MaVILab-UFV/FPVCar_LARS-2025/software/tests/distancia/data/test_03m.csv

timestamp | latencia | fps
1734579958.9551 | 0.04106402397155762 | 5.765084479601648e-10
1734579958.9595 | 0.04106402397155762 | 290.72599986137106
1734579959.0578 | 0.04106402397155762 | 10.174422666407917
1734579959.1672 | 0.04106402397155762 | 9.142657848732023
1734579959.2630 | 0.04106402397155762 | 10.430737857800105
1734579959.3745 | 0.04106402397155762 | 8.973673569376189
1734579959.4856 | 0.04106402397155762 | 9.003318579321773
1734579959.5805 | 0.04106402397155762 | 10.529166488850285
1734579959.7069 | 0.04106402397155762 | 7.913034619375531
1734579959.7789 | 0.015756845474243164 | 13.88276960046074
1734579959.9258 | 0.015756845474243164 | 6.808614529510786
1734579960.0048 | 0.015756845474243164 | 12.659871357985192
1734579960.1151 | 0.015756845474243164 | 9.066569825253127
1734579960.2270 | 0.015756845474243164 | 8.93728585309309
1734579960.3223 | 0.015756845474243164 | 10.487647776599788
1734579960.4328 | 0.015756845474243164 | 9.050625017532427
1734579960.5440 | 0.015756845474243164 | 8.992200463941618
1734579960.6553 | 0.015756845474243164 | 8.990118873594458
1734579960.7493 | 0.015756845474243164 | 10.62855463147385
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
