MaVILab-UFV/FPVCar_LARS-2025/software/tests/distancia/data/test_04m.csv

timestamp | latencia | fps
1734580084.0002 | 0.031940460205078125 | 5.765084063999112e-10
1734580084.0069 | 0.031940460205078125 | 150.04307075910424
1734580084.1037 | 0.031940460205078125 | 10.33504914583092
1734580084.2382 | 0.031940460205078125 | 7.431675709005603
1734580084.2545 | 0.031940460205078125 | 61.56595769665478
1734580084.4295 | 0.031940460205078125 | 5.712084936931931
1734580084.5248 | 0.031940460205078125 | 10.496965510682653
1734580084.6359 | 0.031940460205078125 | 9.000439903779096
1734580084.7469 | 0.031940460205078125 | 9.00944914025497
1734580084.8426 | 0.031940460205078125 | 10.445648708957602
1734580084.8905 | 0.031940460205078125 | 20.874038241412602
1734580085.0506 | 0.031940460205078125 | 6.245752704584205
1734580085.1991 | 0.031270742416381836 | 6.734256965372629
1734580085.2659 | 0.031270742416381836 | 14.987418484572368
1734580085.3809 | 0.031270742416381836 | 8.695759621345154
1734580085.3971 | 0.031270742416381836 | 61.519903781278416
1734580085.5723 | 0.031270742416381836 | 5.708019362854837
1734580085.6675 | 0.031270742416381836 | 10.504089636415545
1734580085.7787 | 0.031270742416381836 | 8.99202696126248
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
