MaVILab-UFV/FPVCar_LARS-2025/software/tests/distancia/data/test_05m.csv

timestamp | latencia | fps
1734580281.2012 | 0.03157162666320801 | 5.765083408578247e-10
1734580281.2151 | 0.03157162666320801 | 72.12160396175803
1734580281.3469 | 0.03157162666320801 | 7.585349797811006
1734580281.4347 | 0.03157162666320801 | 11.389672916864672
1734580281.5637 | 0.03157162666320801 | 7.750451337752162
1734580281.6619 | 0.03157162666320801 | 10.181486282449011
1734580281.7575 | 0.03157162666320801 | 10.462794166803866
1734580281.8525 | 0.03157162666320801 | 10.522905857677602
1734580281.9582 | 0.015758752822875977 | 9.46607445924963
1734580282.0307 | 0.015758752822875977 | 13.785036070530623
1734580282.1301 | 0.015758752822875977 | 10.059609780666515
1734580282.2887 | 0.015758752822875977 | 6.306218858347391
1734580282.3839 | 0.015758752822875977 | 10.50424747555698
1734580282.4952 | 0.015758752822875977 | 8.98773008764223
1734580282.5811 | 0.015758752822875977 | 11.637073906987842
1734580282.6329 | 0.015758752822875977 | 19.299240785901624
1734580282.7345 | 0.015758752822875977 | 9.848303908746605
1734580282.8366 | 0.015758752822875977 | 9.792019872110641
1734580283.0004 | 0.015758752822875977 | 6.10583258362521
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
